mikeysklar/fruitjam-eyespi/fj-eyespi/fj-eyespi.kicad_sch

## KiCad design fj-eyespi/fj-eyespi.kicad_sch (2025-11-08)

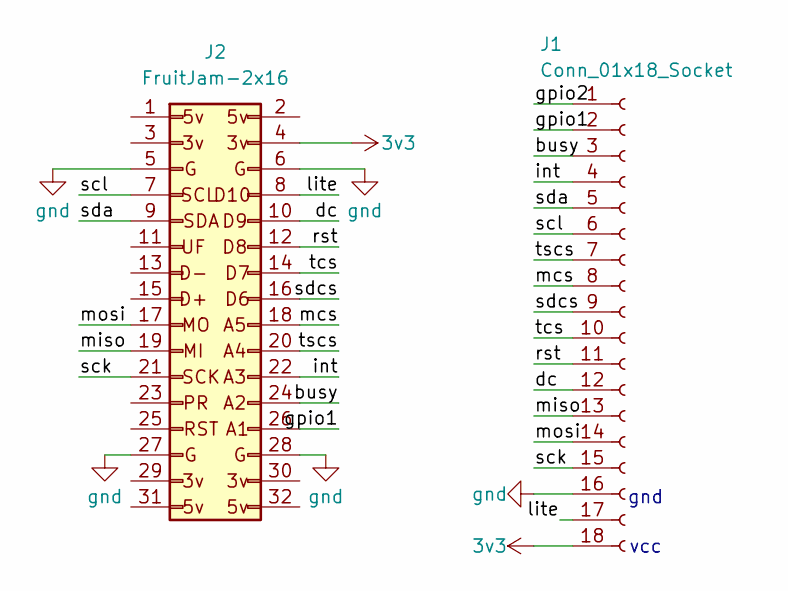
[picture p9: schematic fj-eyespi.kicad_sch]

Parts:
J1: Conn_01x18_Socket; Hirose_FH12-18S-0.5SH_1x18-1MP_P0.50mm_Horizontal
J2: FruitJam-2x16; PinHeader_2x16_P2.54mm_Vertical_SMD

Connections:
3v3: J1.18, J2.4
busy: J1.3, J2.24
dc: J1.12, J2.10
gnd: J1.16, J2.5, J2.6, J2.27, J2.28
gpio1: J1.2, J2.26
gpio2: J1.1
int: J1.4, J2.22
lite: J1.17, J2.8
mcs: J1.8, J2.18
miso: J1.13, J2.19
mosi: J1.14, J2.17
rst: J1.11, J2.12
sck: J1.15, J2.21
scl: J1.6, J2.7
sda: J1.5, J2.9
sdcs: J1.9, J2.16
tcs: J1.10, J2.14
tscs: J1.7, J2.20

Notes on the sheet:
gnd
vcc
